JBlitzar/flopper-one/CAD/br1a.png

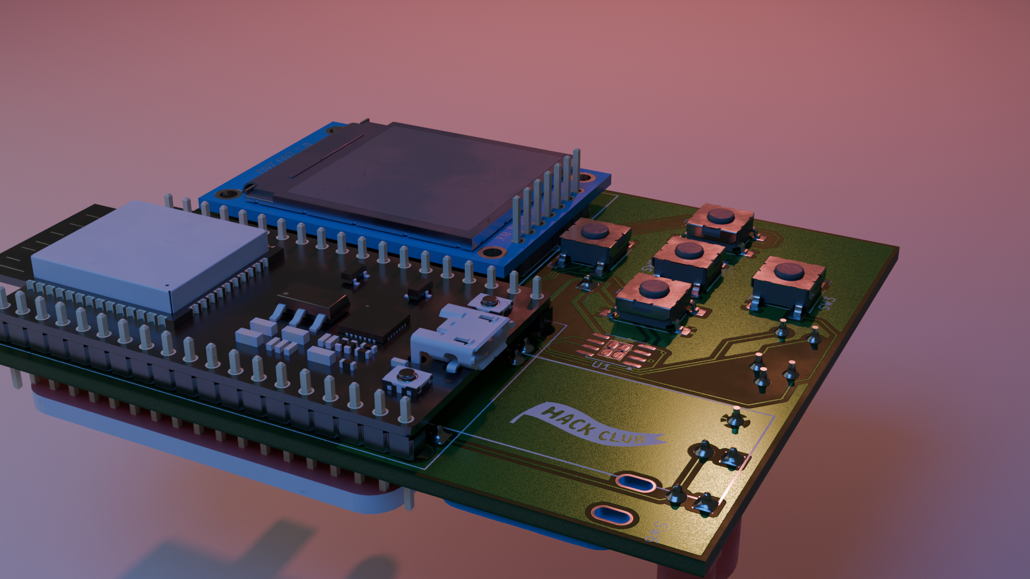
CAD/br1a.png
