JBlitzar/flopper-one/CAD/br2.png

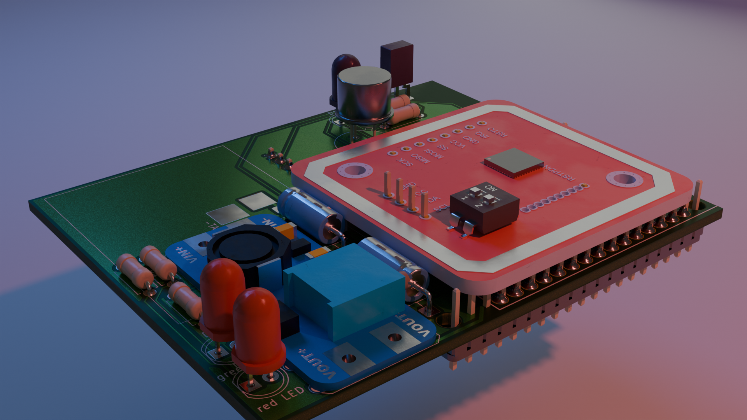
CAD/br2.png
