JBlitzar/flopper-one/PCB/flopper_one/qr.png

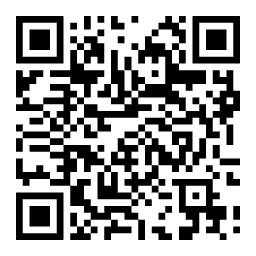
PCB/flopper_one/qr.png
