JBlitzar/flopper-one/PCB/flopper_one/mt3608-1/-font-b-MT3608-b-font-DC-DC-Adjustable-Boost-Module-2A-Boost-Plate-2A-Step.jpg

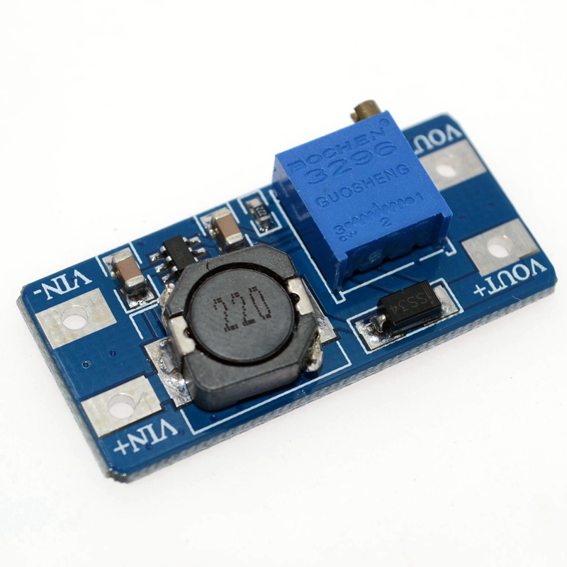
PCB/flopper_one/mt3608-1/-font-b-MT3608-b-font-DC-DC-Adjustable-Boost-Module-2A-Boost-Plate-2A-Step.jpg
