JBlitzar/flopper-one/firmware/flopper-one/include/input_handler.h

#pragma once

#include "input_event.h"

namespace flopper
{

    class InputHandler
    {
    public:
        virtual void on_input(InputEvent event) = 0;
        virtual ~InputHandler() = default;
    };
}
